imciner2/HABET_Burner/Electronics/6-Documentation/Board_Top.png

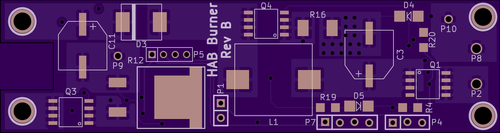
Electronics/6-Documentation/Board_Top.png
