imciner2/HABET_Burner/Electronics/6-Documentation/Schematic-BoostConverter.png

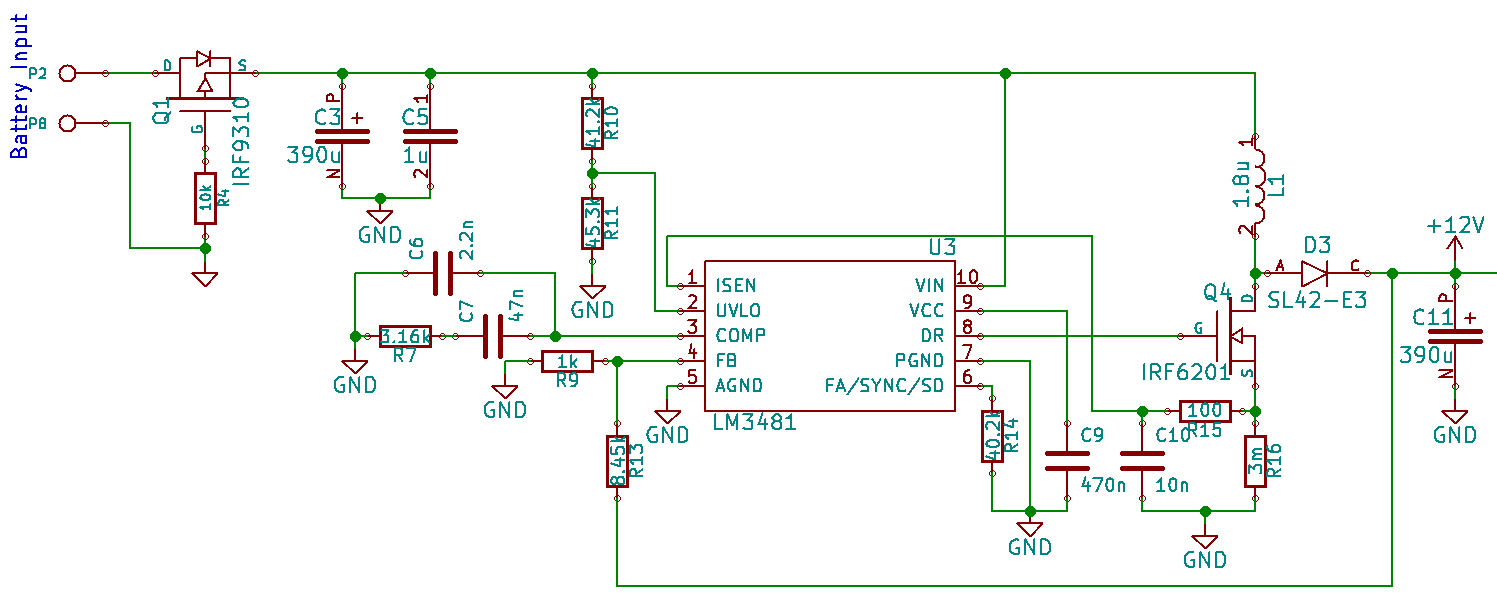
Electronics/6-Documentation/Schematic-BoostConverter.png
