imciner2/HABET_Burner/Electronics/6-Documentation/Schematic-TransconductanceAmplifier.png

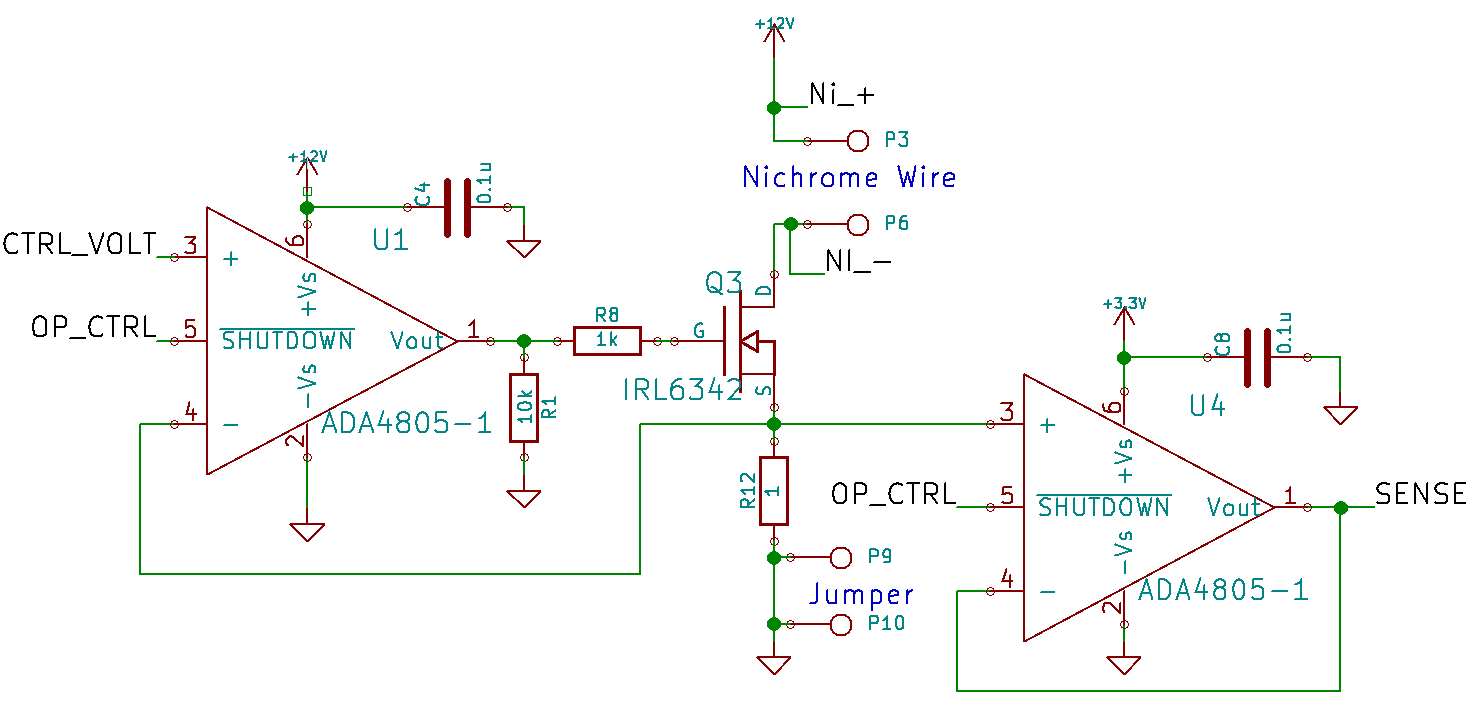
Electronics/6-Documentation/Schematic-TransconductanceAmplifier.png
